newell/nixie-clock-esp32c3/clock/drivers_1.kicad_sch

## KiCad design clock/drivers_1.kicad_sch (2024-07-15)

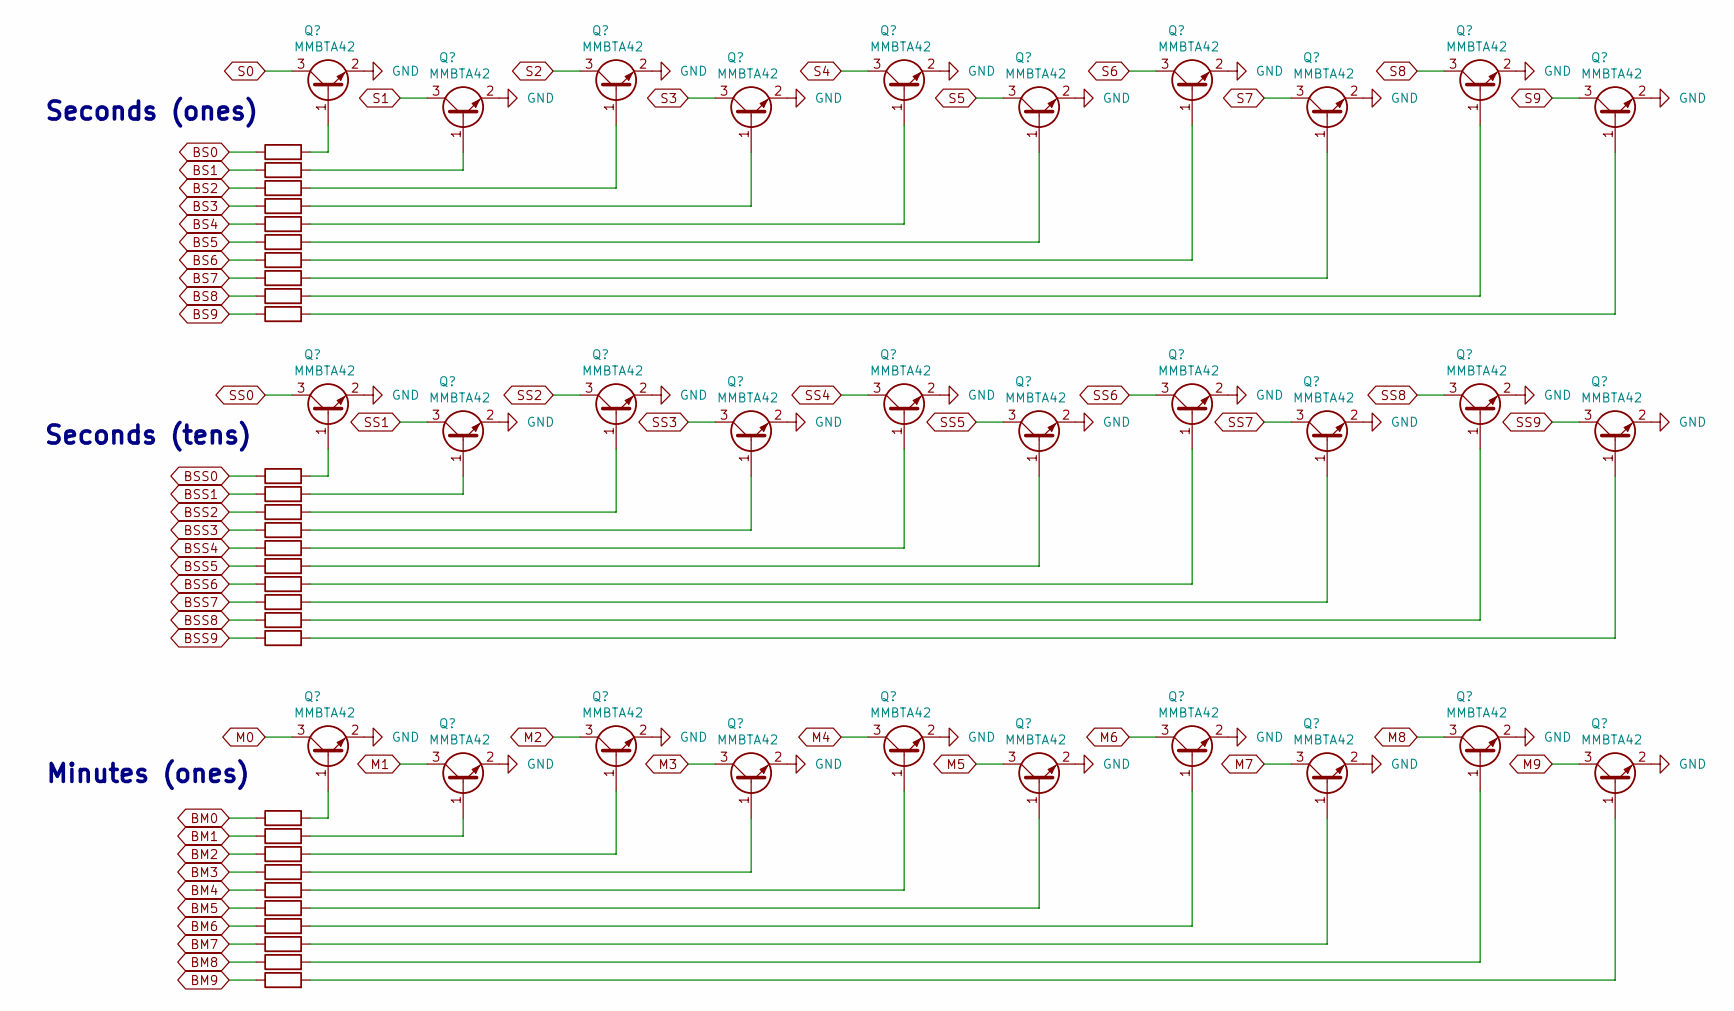
[picture p11: schematic drivers_1.kicad_sch]

Parts:
Q36, Q37, Q38, Q39, Q40, Q41, Q42, Q43, Q44, Q45, Q46, Q47, Q48, Q49, Q50, Q51, Q52, Q53, Q54, Q55, Q56, Q57, Q58, Q59, Q60, Q61, Q62, Q63, Q64, Q65: MMBTA42; SOT-23
R57, R58, R59, R60, R61, R62, R63, R64, R65, R66, R67, R68, R69, R70, R71, R72, R73, R74, R75, R76, R77, R78, R79, R80, R81, R82, R83, R84, R85, R86: 10k; R_0805_2012Metric_Pad1.20x1.40mm_HandSolder; Manufacturer_Part_Number RC0805FR-0710KL

Connections:
BM0: R77.1
BM1: R78.1
BM2: R79.1
BM3: R80.1
BM4: R81.1
BM5: R82.1
BM6: R83.1
BM7: R84.1
BM8: R85.1
BM9: R86.1
BS0: R57.1
BS1: R58.1
BS2: R59.1
BS3: R60.1
BS4: R61.1
BS5: R62.1
BS6: R63.1
BS7: R64.1
BS8: R65.1
BS9: R66.1
BSS0: R67.1
BSS1: R68.1
BSS2: R69.1
BSS3: R70.1
BSS4: R71.1
BSS5: R72.1
BSS6: R73.1
BSS7: R74.1
BSS8: R75.1
BSS9: R76.1
GND: Q36.2 (E), Q37.2 (E), Q38.2 (E), Q39.2 (E), Q40.2 (E), Q41.2 (E), Q42.2 (E), Q43.2 (E), Q44.2 (E), Q45.2 (E), Q46.2 (E), Q47.2 (E), Q48.2 (E), Q49.2 (E), Q50.2 (E), Q51.2 (E), Q52.2 (E), Q53.2 (E), Q54.2 (E), Q55.2 (E), Q56.2 (E), Q57.2 (E), Q58.2 (E), Q59.2 (E), Q60.2 (E), Q61.2 (E), Q62.2 (E), Q63.2 (E), Q64.2 (E), Q65.2 (E)
M0: Q38.3 (C)
M1: Q41.3 (C)
M2: Q44.3 (C)
M3: Q47.3 (C)
M4: Q50.3 (C)
M5: Q53.3 (C)
M6: Q56.3 (C)
M7: Q59.3 (C)
M8: Q62.3 (C)
M9: Q65.3 (C)
unnamed: Q36.1 (B), R57.2
unnamed: Q37.1 (B), R67.2
unnamed: Q38.1 (B), R77.2
unnamed: Q39.1 (B), R58.2
unnamed: Q40.1 (B), R68.2
unnamed: Q41.1 (B), R78.2
unnamed: Q42.1 (B), R59.2
unnamed: Q43.1 (B), R69.2
unnamed: Q44.1 (B), R79.2
unnamed: Q45.1 (B), R60.2
unnamed: Q46.1 (B), R70.2
unnamed: Q47.1 (B), R80.2
unnamed: Q48.1 (B), R61.2
unnamed: Q49.1 (B), R71.2
unnamed: Q50.1 (B), R81.2
unnamed: Q51.1 (B), R62.2
unnamed: Q52.1 (B), R72.2
unnamed: Q53.1 (B), R82.2
unnamed: Q54.1 (B), R63.2
unnamed: Q55.1 (B), R73.2
unnamed: Q56.1 (B), R83.2
unnamed: Q57.1 (B), R64.2
unnamed: Q58.1 (B), R74.2
unnamed: Q59.1 (B), R84.2
unnamed: Q60.1 (B), R65.2
unnamed: Q61.1 (B), R75.2
unnamed: Q62.1 (B), R85.2
unnamed: Q63.1 (B), R66.2
unnamed: Q64.1 (B), R76.2
unnamed: Q65.1 (B), R86.2
S0: Q36.3 (C)
S1: Q39.3 (C)
S2: Q42.3 (C)
S3: Q45.3 (C)
S4: Q48.3 (C)
S5: Q51.3 (C)
S6: Q54.3 (C)
S7: Q57.3 (C)
S8: Q60.3 (C)
S9: Q63.3 (C)
SS0: Q37.3 (C)
SS1: Q40.3 (C)
SS2: Q43.3 (C)
SS3: Q46.3 (C)
SS4: Q49.3 (C)
SS5: Q52.3 (C)
SS6: Q55.3 (C)
SS7: Q58.3 (C)
SS8: Q61.3 (C)
SS9: Q64.3 (C)

Notes on the sheet:
Minutes (ones)
Seconds (ones)
Seconds (tens)
