newell/nixie-clock-esp32c3/clock/drivers_2.kicad_sch

## KiCad design clock/drivers_2.kicad_sch (2024-07-15)

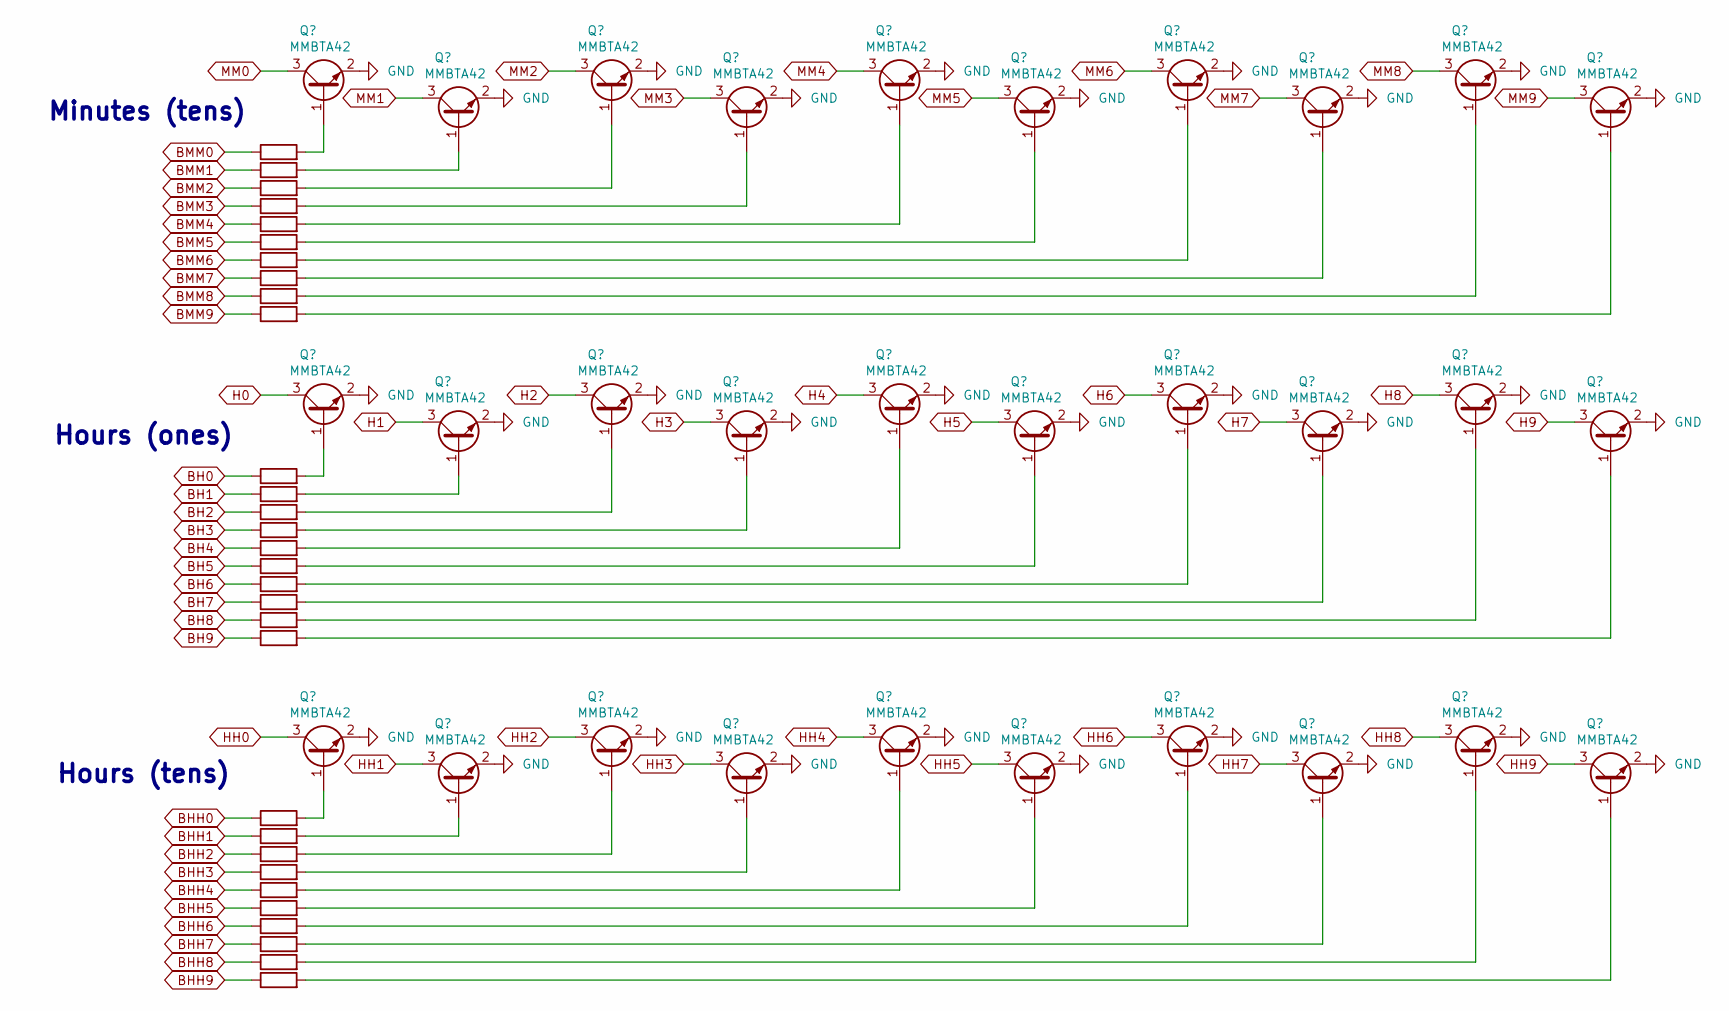
[picture p12: schematic drivers_2.kicad_sch]

Parts:
Q1, Q2, Q3, Q4, Q5, Q6, Q7, Q8, Q9, Q10, Q11, Q12, Q13, Q14, Q15, Q16, Q17, Q18, Q19, Q20, Q21, Q22, Q23, Q24, Q25, Q26, Q27, Q28, Q29, Q30: MMBTA42; SOT-23
R9, R10, R11, R12, R13, R14, R15, R16, R17, R18, R19, R20, R21, R22, R23, R24, R25, R26, R27, R28, R29, R30, R31, R32, R33, R34, R35, R36, R37, R38: 10k; R_0805_2012Metric_Pad1.20x1.40mm_HandSolder; Manufacturer_Part_Number RC0805FR-0710KL

Connections:
BH0: R19.1
BH1: R20.1
BH2: R21.1
BH3: R22.1
BH4: R23.1
BH5: R24.1
BH6: R25.1
BH7: R26.1
BH8: R27.1
BH9: R28.1
BHH0: R29.1
BHH1: R30.1
BHH2: R31.1
BHH3: R32.1
BHH4: R33.1
BHH5: R34.1
BHH6: R35.1
BHH7: R36.1
BHH8: R37.1
BHH9: R38.1
BMM0: R9.1
BMM1: R10.1
BMM2: R11.1
BMM3: R12.1
BMM4: R13.1
BMM5: R14.1
BMM6: R15.1
BMM7: R16.1
BMM8: R17.1
BMM9: R18.1
GND: Q1.2 (E), Q2.2 (E), Q3.2 (E), Q4.2 (E), Q5.2 (E), Q6.2 (E), Q7.2 (E), Q8.2 (E), Q9.2 (E), Q10.2 (E), Q11.2 (E), Q12.2 (E), Q13.2 (E), Q14.2 (E), Q15.2 (E), Q16.2 (E), Q17.2 (E), Q18.2 (E), Q19.2 (E), Q20.2 (E), Q21.2 (E), Q22.2 (E), Q23.2 (E), Q24.2 (E), Q25.2 (E), Q26.2 (E), Q27.2 (E), Q28.2 (E), Q29.2 (E), Q30.2 (E)
H0: Q2.3 (C)
H1: Q5.3 (C)
H2: Q8.3 (C)
H3: Q11.3 (C)
H4: Q14.3 (C)
H5: Q17.3 (C)
H6: Q20.3 (C)
H7: Q23.3 (C)
H8: Q26.3 (C)
H9: Q29.3 (C)
HH0: Q3.3 (C)
HH1: Q6.3 (C)
HH2: Q9.3 (C)
HH3: Q12.3 (C)
HH4: Q15.3 (C)
HH5: Q18.3 (C)
HH6: Q21.3 (C)
HH7: Q24.3 (C)
HH8: Q27.3 (C)
HH9: Q30.3 (C)
MM0: Q1.3 (C)
MM1: Q4.3 (C)
MM2: Q7.3 (C)
MM3: Q10.3 (C)
MM4: Q13.3 (C)
MM5: Q16.3 (C)
MM6: Q19.3 (C)
MM7: Q22.3 (C)
MM8: Q25.3 (C)
MM9: Q28.3 (C)
unnamed: Q1.1 (B), R9.2
unnamed: Q2.1 (B), R19.2
unnamed: Q3.1 (B), R29.2
unnamed: Q4.1 (B), R10.2
unnamed: Q5.1 (B), R20.2
unnamed: Q6.1 (B), R30.2
unnamed: Q7.1 (B), R11.2
unnamed: Q8.1 (B), R21.2
unnamed: Q9.1 (B), R31.2
unnamed: Q10.1 (B), R12.2
unnamed: Q11.1 (B), R22.2
unnamed: Q12.1 (B), R32.2
unnamed: Q13.1 (B), R13.2
unnamed: Q14.1 (B), R23.2
unnamed: Q15.1 (B), R33.2
unnamed: Q16.1 (B), R14.2
unnamed: Q17.1 (B), R24.2
unnamed: Q18.1 (B), R34.2
unnamed: Q19.1 (B), R15.2
unnamed: Q20.1 (B), R25.2
unnamed: Q21.1 (B), R35.2
unnamed: Q22.1 (B), R16.2
unnamed: Q23.1 (B), R26.2
unnamed: Q24.1 (B), R36.2
unnamed: Q25.1 (B), R17.2
unnamed: Q26.1 (B), R27.2
unnamed: Q27.1 (B), R37.2
unnamed: Q28.1 (B), R18.2
unnamed: Q29.1 (B), R28.2
unnamed: Q30.1 (B), R38.2

Notes on the sheet:
Hours (tens)
Hours (ones)
Minutes (tens)
