newell/nixie-clock-esp32c3/clock/esp32-c3.kicad_sch

## KiCad design clock/esp32-c3.kicad_sch (2024-07-15)

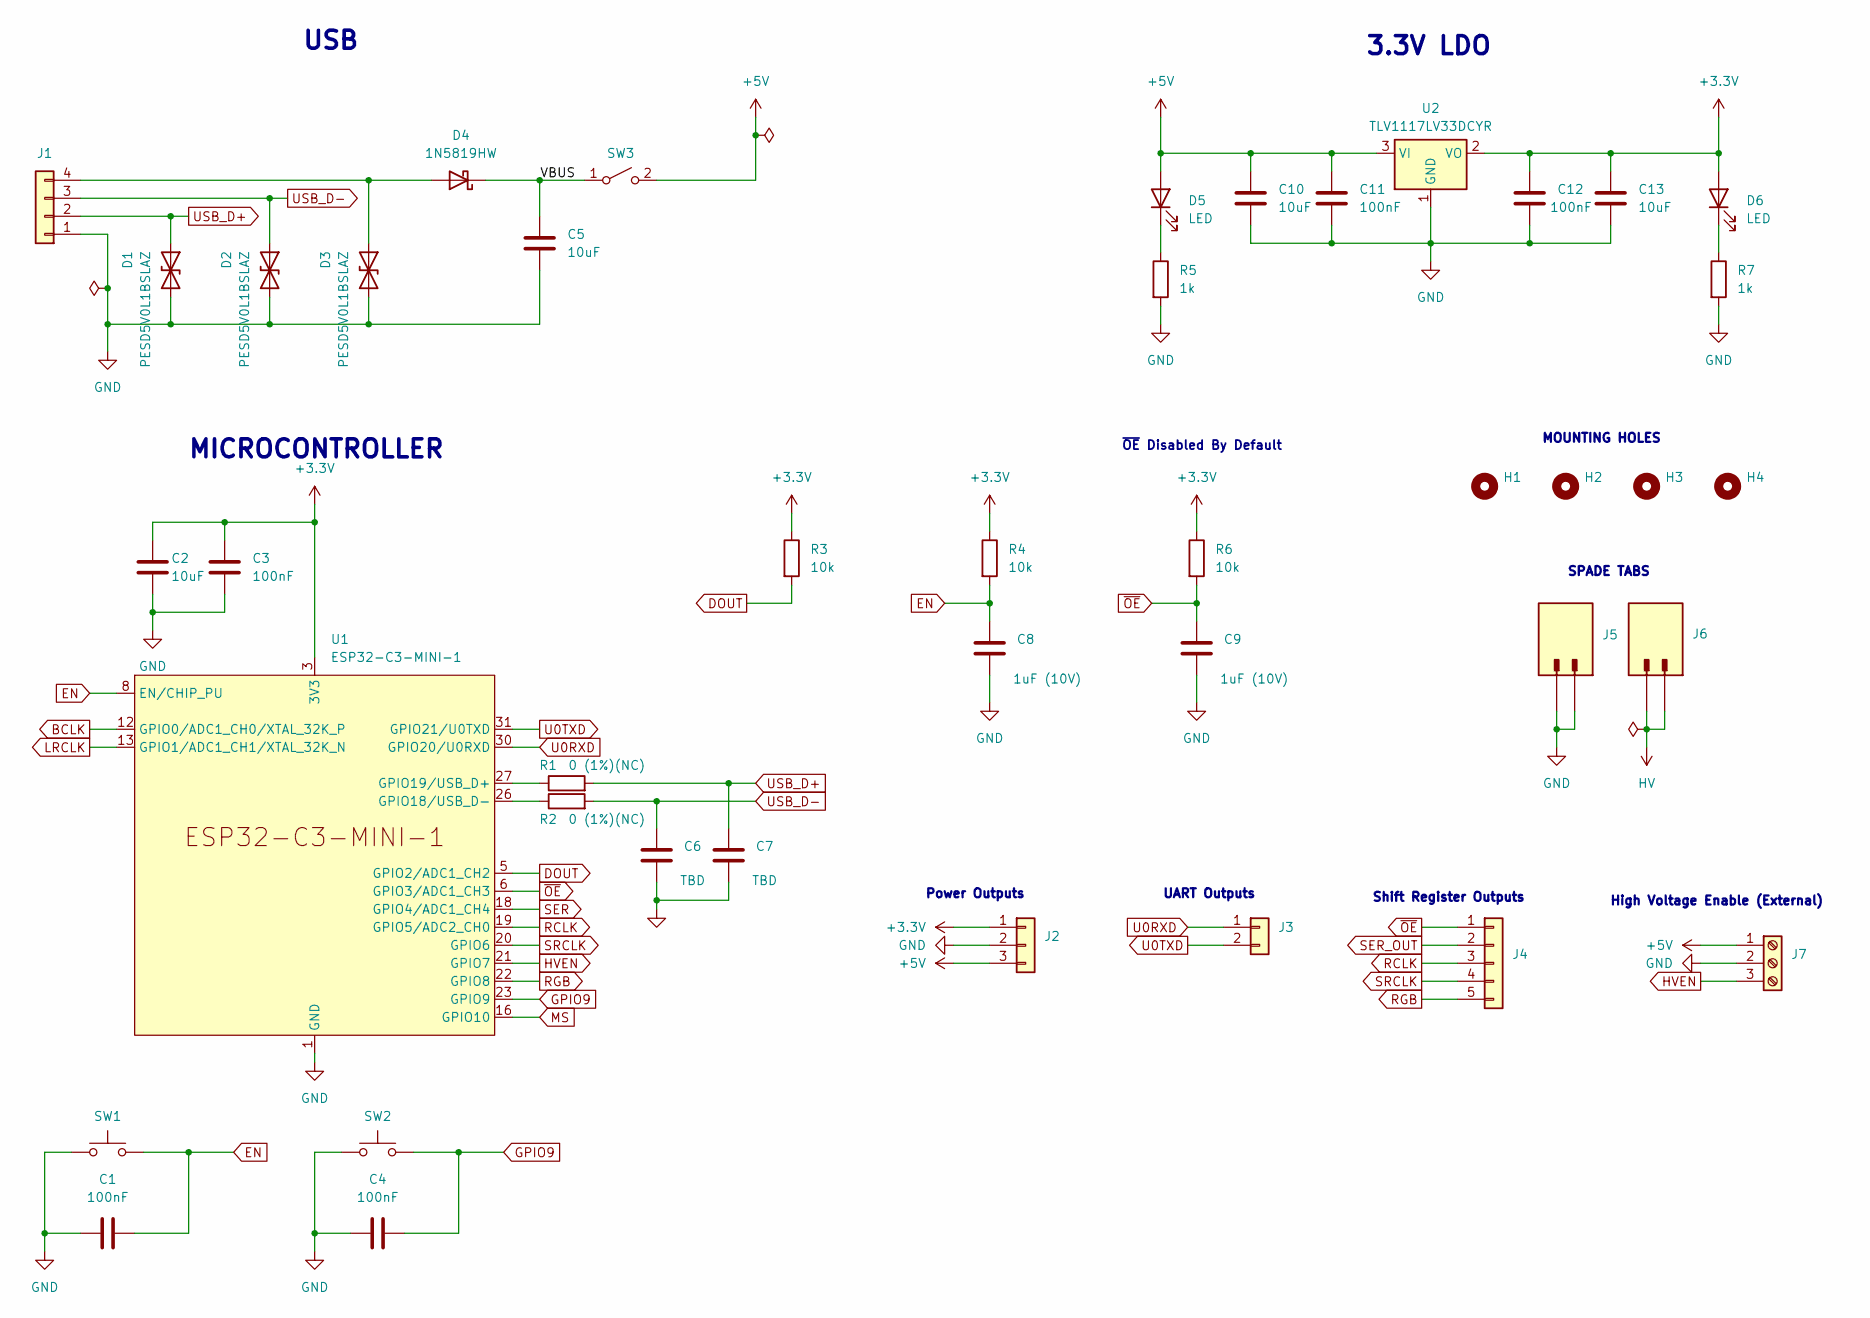
[picture p13: schematic esp32-c3.kicad_sch]

Parts:
C1, C3, C4, C11, C12: 100nF; C_0805_2012Metric_Pad1.18x1.45mm_HandSolder; Manufacturer_Part_Number CC0805JRX7R9BB104
C2, C5, C10, C13: 10uF; C_0805_2012Metric_Pad1.18x1.45mm_HandSolder; Manufacturer_Part_Number CC0805KKX5R6BB106
C6, C7: TBD; C_0805_2012Metric_Pad1.18x1.45mm_HandSolder
C8, C9: 1uF (10V); C_0805_2012Metric_Pad1.18x1.45mm_HandSolder; Manufacturer_Part_Number GRM21BR71C105KA01L
D1, D2, D3: PESD5V0L1BSLAZ; D_SOD-882; Manufacturer_Part_Number PESD5V0L1BSLAZ
D4: 1N5819HW; D_SOD-123; Manufacturer_Part_Number 1N5819HW-7-F
D5: LED; LED_0603_1608Metric_Pad1.05x0.95mm_HandSolder
D6: LED; LED_0603_1608Metric_Pad1.05x0.95mm_HandSolder; Mouser Part Number 710-150080RS75000
H1, H2, H3, H4: MountingHole; MountingHole_3.2mm_M3_ISO7380_Pad_TopBottom
J1: Conn_01x04; JST_PH_B4B-PH-K_1x04_P2.00mm_Vertical
J2: Conn_01x03; PinHeader_1x03_P2.54mm_Vertical
J3: Conn_01x02; PinHeader_1x02_P2.54mm_Vertical
J4: Conn_01x05; PinHeader_1x05_P2.54mm_Vertical
J5, J6: KEYSTONE_1287; PARTREV F
J7: Screw_Terminal_01x03; TerminalBlock_Phoenix_MKDS-1,5-3_1x03_P5.00mm_Horizontal
R1, R2: 0 (1%)(NC); R_0805_2012Metric_Pad1.20x1.40mm_HandSolder; Manufacturer_Part_Number RC0805FR-130RL
R3, R4, R6: 10k; R_0805_2012Metric_Pad1.20x1.40mm_HandSolder; Manufacturer_Part_Number RC0805FR-0710KL
R5, R7: 1k; R_0805_2012Metric_Pad1.20x1.40mm_HandSolder; Manufacturer_Part_Number RC0805FR-071KL
SW1, SW2: SW_Push; SW_Tactile_SPST_NO_Straight_CK_PTS636Sx25SMTRLFS
SW3: SW_SPST; SolderWire-0.75sqmm_1x02_P4.8mm_D1.25mm_OD2.3mm
U1: ESP32-C3-MINI-1; ESP32-C3-MINI-1_HandSoldering; Manufacturer_Part_Number ESP32-C3-MINI-1-N4
U2: TLV1117LV33DCYR; SOT-223; Manufacturer_Part_Number TLV1117LV33DCYR

Connections:
+3.3V: C2.1, C3.1, C12.1, C13.1, D6.2 (A), J2.1, R3.1, R4.1, R6.1, U1.3 (3V3), U2.2 (VO)
+5V: C10.1, C11.1, D5.2 (A), J2.3, J7.1, SW3.2 (B), U2.3 (VI)
BCLK: U1.12 (GPIO0/ADC1_CH0/XTAL_32K_P)
DOUT: R3.2, U1.5 (GPIO2/ADC1_CH2)
EN: C1.1, C8.2, R4.2, SW1.2, U1.8 (EN/CHIP_PU)
GND: C1.2, C2.2, C3.2, C4.2, C5.2, C6.1, C7.1, C8.1, C9.1, C10.2, C11.2, C12.2, C13.2, D1.2 (A2), D2.2 (A2), D3.2 (A2), J1.1, J2.2, J5.1_1, J5.1_2, J7.2, R5.2, R7.2, SW1.1, SW2.1, U1.1 (GND), U1.2 (GND), U1.11 (GND), U1.14 (GND), U1.36 (GND), U1.37 (GND), U1.38 (GND), U1.39 (GND), U1.40 (GND), U1.41 (GND), U1.42 (GND), U1.43 (GND), U1.44 (GND), U1.45 (GND), U1.46 (GND), U1.47 (GND), U1.48 (GND), U1.49 (GND), U1.50 (GND), U1.51 (GND), U1.52 (GND), U1.53 (GND), U2.1 (GND)
GPIO9: C4.1, SW2.2, U1.23 (GPIO9)
HV: J6.1_1, J6.1_2
HVEN: J7.3, U1.21 (GPIO7)
LRCLK: U1.13 (GPIO1/ADC1_CH1/XTAL_32K_N)
MS: U1.16 (GPIO10)
unnamed: D3.1 (A1), D4.2 (A), J1.4
unnamed: D5.1 (K), R5.1
unnamed: D6.1 (K), R7.1
unnamed: R1.1, U1.27 (GPIO19/USB_D+)
unnamed: R2.1, U1.26 (GPIO18/USB_D-)
RCLK: J4.3, U1.19 (GPIO5/ADC2_CH0)
RGB: J4.5, U1.22 (GPIO8)
SER: U1.18 (GPIO4/ADC1_CH4)
SER_OUT: J4.2
SRCLK: J4.4, U1.20 (GPIO6)
U0RXD: J3.1, U1.30 (GPIO20/U0RXD)
U0TXD: J3.2, U1.31 (GPIO21/U0TXD)
USB_D+: C7.2, D1.1 (A1), J1.2, R1.2
USB_D-: C6.2, D2.1 (A1), J1.3, R2.2
VBUS: C5.1, D4.1 (K), SW3.1 (A)
~OE: C9.2, J4.1, R6.2, U1.6 (GPIO3/ADC1_CH3)

Notes on the sheet:
USB
3.3V LDO
SPADE TABS
High Voltage Enable (External)
MOUNTING HOLES
Shift Register Outputs
Power Outputs
UART Outputs
MICROCONTROLLER
~{OE} Disabled By Default
