newell/nixie-clock-esp32c3/clock/nixie_tubes.kicad_sch

## KiCad design clock/nixie_tubes.kicad_sch (2024-07-15)

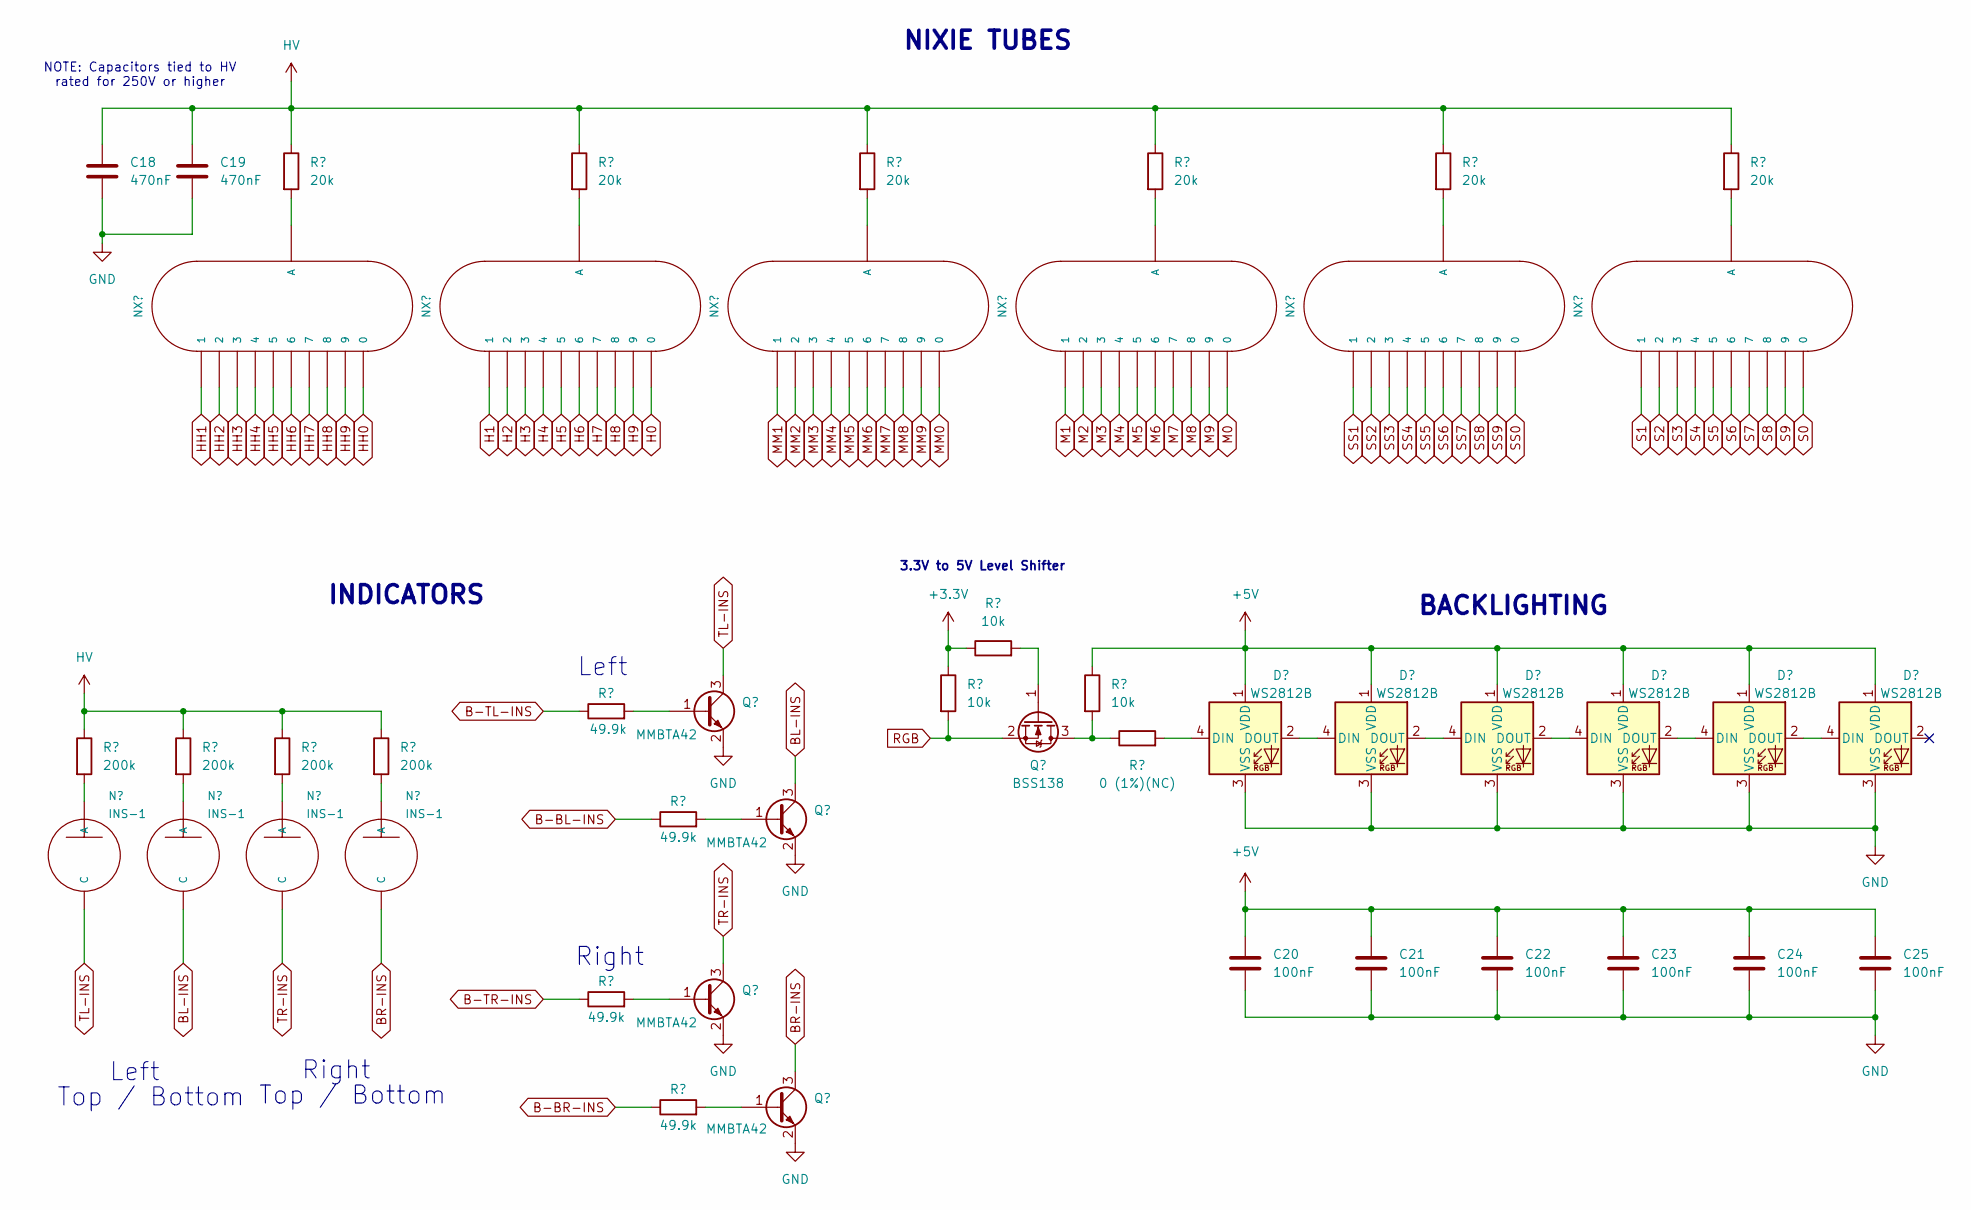
[picture p14: schematic nixie_tubes.kicad_sch]

Parts:
C18, C19: 470nF; C_1812_4532Metric_Pad1.57x3.40mm_HandSolder; Manufacturer_Part_Number CC0805JRX7R9BB104
C20, C21, C22, C23, C24, C25: 100nF; C_0805_2012Metric_Pad1.18x1.45mm_HandSolder; Manufacturer_Part_Number CC0805JRX7R9BB104
D7, D8, D9, D10, D11, D12: WS2812B; LED_WS2812B_PLCC4_5.0x5.0mm_P3.2mm
N1, N2, N3, N4: INS-1; mynixies-INS-1
NX1, NX2, NX3, NX4, NX5, NX6: IN-12A; nixies-us-IN-12-DSUB-NOHOLE
Q31, Q32, Q33, Q34: MMBTA42; SOT-23
Q35: BSS138; SOT-23; Manufacturer_Part_Number BSS138
R39, R40, R41, R43: 200k; R_0805_2012Metric_Pad1.20x1.40mm_HandSolder; Manufacturer_Part_Number RC0805FR-07200KL
R42, R44, R49, R54, R55, R56: 20k; R_0805_2012Metric_Pad1.20x1.40mm_HandSolder; Manufacturer_Part_Number RC0805JR-0720KL
R45, R46, R47, R48: 49.9k; R_0805_2012Metric_Pad1.20x1.40mm_HandSolder; Manufacturer_Part_Number RC0805FR-0749K9L
R50, R51, R52: 10k; R_0805_2012Metric_Pad1.20x1.40mm_HandSolder; Manufacturer_Part_Number RC0805FR-0710KL
R53: 0 (1%)(NC); R_0805_2012Metric_Pad1.20x1.40mm_HandSolder; Manufacturer_Part_Number RC0805FR-130RL

Connections:
+3.3V: R50.1, R51.1
+5V: C20.1, C21.1, C22.1, C23.1, C24.1, C25.1, D7.1 (VDD), D8.1 (VDD), D9.1 (VDD), D10.1 (VDD), D11.1 (VDD), D12.1 (VDD), R52.1
B-BL-INS: R47.1
B-BR-INS: R48.1
B-TL-INS: R45.1
B-TR-INS: R46.1
BL-INS: N2.P$1 (C), Q33.3 (C)
BR-INS: N4.P$1 (C), Q34.3 (C)
GND: C18.2, C19.2, C20.2, C21.2, C22.2, C23.2, C24.2, C25.2, D7.3 (VSS), D8.3 (VSS), D9.3 (VSS), D10.3 (VSS), D11.3 (VSS), D12.3 (VSS), Q31.2 (E), Q32.2 (E), Q33.2 (E), Q34.2 (E)
H0: NX2.0
H1: NX2.1
H2: NX2.2
H3: NX2.3
H4: NX2.4
H5: NX2.5
H6: NX2.6
H7: NX2.7
H8: NX2.8
H9: NX2.9
HH0: NX1.0
HH1: NX1.1
HH2: NX1.2
HH3: NX1.3
HH4: NX1.4
HH5: NX1.5
HH6: NX1.6
HH7: NX1.7
HH8: NX1.8
HH9: NX1.9
HV: C18.1, C19.1, R39.1, R40.1, R41.1, R42.1, R43.1, R44.1, R49.1, R54.1, R55.1, R56.1
M0: NX4.0
M1: NX4.1
M2: NX4.2
M3: NX4.3
M4: NX4.4
M5: NX4.5
M6: NX4.6
M7: NX4.7
M8: NX4.8
M9: NX4.9
MM0: NX3.0
MM1: NX3.1
MM2: NX3.2
MM3: NX3.3
MM4: NX3.4
MM5: NX3.5
MM6: NX3.6
MM7: NX3.7
MM8: NX3.8
MM9: NX3.9
unnamed: D7.2 (DOUT), D8.4 (DIN)
unnamed: D7.4 (DIN), R53.2
unnamed: D8.2 (DOUT), D9.4 (DIN)
unnamed: D10.2 (DOUT), D11.4 (DIN)
unnamed: D9.2 (DOUT), D10.4 (DIN)
unnamed: D11.2 (DOUT), D12.4 (DIN)
unnamed: N1.P$2 (A), R39.2
unnamed: N2.P$2 (A), R40.2
unnamed: N3.P$2 (A), R41.2
unnamed: N4.P$2 (A), R43.2
unnamed: NX1.A, R42.2
unnamed: NX2.A, R44.2
unnamed: NX3.A, R49.2
unnamed: NX4.A, R54.2
unnamed: NX5.A, R55.2
unnamed: NX6.A, R56.2
unnamed: Q31.1 (B), R45.2
unnamed: Q32.1 (B), R46.2
unnamed: Q33.1 (B), R47.2
unnamed: Q34.1 (B), R48.2
unnamed: Q35.1 (G), R51.2
unnamed: Q35.3 (D), R52.2, R53.1
RGB: Q35.2 (S), R50.2
S0: NX6.0
S1: NX6.1
S2: NX6.2
S3: NX6.3
S4: NX6.4
S5: NX6.5
S6: NX6.6
S7: NX6.7
S8: NX6.8
S9: NX6.9
SS0: NX5.0
SS1: NX5.1
SS2: NX5.2
SS3: NX5.3
SS4: NX5.4
SS5: NX5.5
SS6: NX5.6
SS7: NX5.7
SS8: NX5.8
SS9: NX5.9
TL-INS: N1.P$1 (C), Q31.3 (C)
TR-INS: N3.P$1 (C), Q32.3 (C)

Notes on the sheet:
3.3V to 5V Level Shifter
Right
BACKLIGHTING
Left
NOTE: Capacitors tied to HV rated for 250V or higher
Top / Bottom
INDICATORS
NIXIE TUBES
