newell/nixie-clock-esp32c3/clock/power.kicad_sch

## KiCad design clock/power.kicad_sch (2024-07-15)

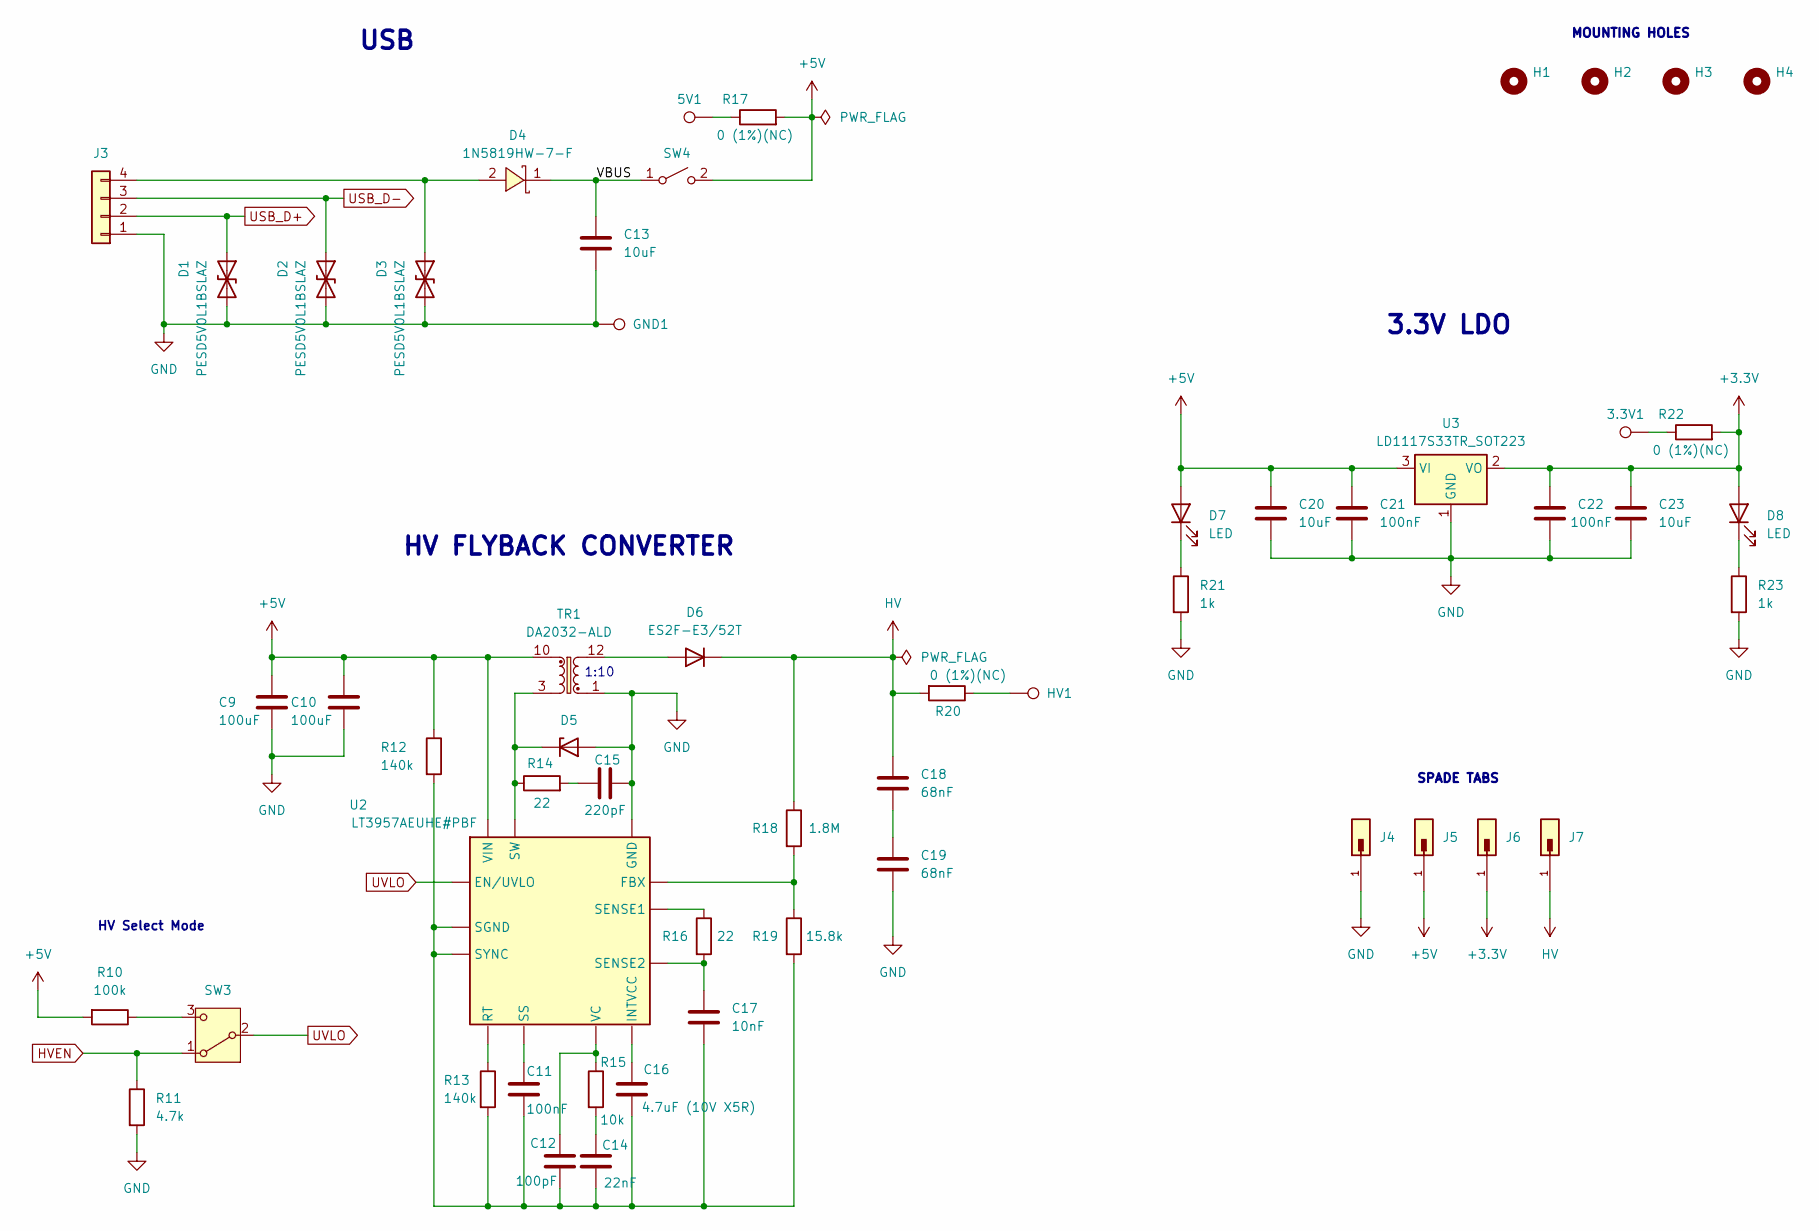
[picture p15: schematic power.kicad_sch]

Parts:
3.3V1, 5V1: TestPoint; TestPoint_Pad_D1.0mm
C9, C10: 100uF; GRM31x
C11, C21, C22: 100nF; C_0805_2012Metric_Pad1.18x1.45mm_HandSolder
C12: 100pF; C_0805_2012Metric_Pad1.18x1.45mm_HandSolder
C13, C20, C23: 10uF; C_0805_2012Metric_Pad1.18x1.45mm_HandSolder
C14: 22nF; C_0805_2012Metric_Pad1.18x1.45mm_HandSolder
C15: 220pF; C_0805_2012Metric_Pad1.18x1.45mm_HandSolder
C16: 4.7uF (10V X5R); C_0805_2012Metric_Pad1.18x1.45mm_HandSolder
C17: 10nF; C_0805_2012Metric_Pad1.18x1.45mm_HandSolder
C18, C19: 68nF; GRM43x; Mouser Part Number 81-GRM43QR72J683KW01
D1, D2, D3: PESD5V0L1BSLAZ; D_SOD-882
D4: 1N5819HW-7-F; D_SOD-123F; LCSC Part C82544
D5: MMSZ5258B; D_SOD-123F
D6: ES2F-E3/52T; D_SMB_Handsoldering
D7: LED; LED_0603_1608Metric_Pad1.05x0.95mm_HandSolder
D8: LED; LED_0603_1608Metric_Pad1.05x0.95mm_HandSolder; Mouser Part Number 710-150080RS75000
GND1: TestPoint; TestPoint_Pad_D1.0mm
H1, H2, H3, H4: MountingHole; MountingHole_3.2mm_M3_ISO7380_Pad_TopBottom
HV1: TestPoint; TestPoint_Pad_D1.0mm
J3: Conn_01x04; JST_PH_B4B-PH-K_1x04_P2.00mm_Vertical
J4, J5, J6, J7: KEYSTONE_spade_tab; PARTREV D
R10: 100k; R_0805_2012Metric_Pad1.20x1.40mm_HandSolder
R11: 4.7k; R_0805_2012Metric_Pad1.20x1.40mm_HandSolder
R12, R13: 140k; R_0805_2012Metric_Pad1.20x1.40mm_HandSolder
R14, R16: 22; R_0805_2012Metric_Pad1.20x1.40mm_HandSolder
R15: 10k; R_0805_2012Metric_Pad1.20x1.40mm_HandSolder
R17, R20, R22: 0 (1%)(NC); R_0805_2012Metric_Pad1.20x1.40mm_HandSolder
R18: 1.8M; RESC3116X65N; Mouser Part Number 603-RC1206FR-071M8L
R19: 15.8k; R_0805_2012Metric_Pad1.20x1.40mm_HandSolder
R21, R23: 1k; R_0805_2012Metric_Pad1.20x1.40mm_HandSolder
SW3: SW_SPDT; SW_SPDT_PCM12
SW4: SW_SPST; SolderWire-0.75sqmm_1x02_P4.8mm_D1.25mm_OD2.3mm
TR1: DA2032-ALD; SOP250P2197X889-12N
U2: LT3957AEUHE#PBF; LT3958EUHETRPBF; Manufacturer_Part_Number LT3957AEUHE#PBF
U3: LD1117S33TR_SOT223; TO-220-3_Vertical

Connections:
+3.3V: C22.1, C23.1, D8.2 (A), J6.1, R22.2, U3.2 (VO)
+5V: C9.1, C10.1, C20.1, C21.1, D7.2 (A), J5.1, R10.2, R12.1, R17.2, SW4.2 (B), TR1.7, TR1.8, TR1.9, TR1.10, U2.27 (VIN), U3.3 (VI)
GND: C9.2, C10.2, C13.2, C15.2, C19.2, C20.2, C21.2, C22.2, C23.2, D1.2 (A2), D2.2 (A2), D3.2 (A2), D5.2 (A), GND1.1, J3.1, J4.1, R11.2, R21.2, R23.2, TR1.1, U2.12 (GND), U2.13 (GND), U2.14 (GND), U2.15 (GND), U2.16 (GND), U2.17 (GND), U3.1 (GND)
HV: C18.1, D6.1 (K), J7.1, R18.1, R20.2
HVEN: R11.1, SW3.1 (A)
unnamed: 3.3V1.1, R22.1
unnamed: 5V1.1, R17.1
unnamed: C11.1, U2.32 (SS)
unnamed: C11.2, C12.2, C14.2, C16.2, C17.2, R12.2, R13.2, R19.2, U2.4 (SGND), U2.23 (SGND), U2.24 (SGND), U2.34 (SYNC), U2.37 (SGND)
unnamed: C12.1, R15.1, U2.30 (VC)
unnamed: C14.1, R15.2
unnamed: C15.1, R14.2
unnamed: C16.1, U2.28 (INTVCC)
unnamed: C17.1, R16.2, U2.3 (SENSE2)
unnamed: C18.2, C19.1
unnamed: D3.1 (A1), D4.2 (A), J3.4
unnamed: D5.1 (K), R14.1, TR1.3, TR1.4, TR1.5, TR1.6, U2.8 (SW), U2.9 (SW), U2.20 (SW), U2.21 (SW), U2.38 (SW)
unnamed: D6.2 (A), TR1.12
unnamed: D7.1 (K), R21.1
unnamed: D8.1 (K), R23.1
unnamed: HV1.1, R20.1
unnamed: R10.1, SW3.3 (C)
unnamed: R13.1, U2.33 (RT)
unnamed: R16.1, U2.6 (SENSE1)
unnamed: R18.2, R19.1, U2.31 (FBX)
unnamed: U2.1 (NC), U2.2 (NC), U2.10 (NC), U2.35 (NC), U2.36 (NC)
USB_D+: D1.1 (A1), J3.2
USB_D-: D2.1 (A1), J3.3
UVLO: SW3.2 (B), U2.25 (EN/UVLO)
VBUS: C13.1, D4.1 (K), SW4.1 (A)

Notes on the sheet:
MOUNTING HOLES
3.3V LDO
1:10
HV Select Mode
USB
SPADE TABS
HV FLYBACK CONVERTER
