newell/nixie-clock-esp32c3/clock/shift_registers.kicad_sch

## KiCad design clock/shift_registers.kicad_sch (2024-07-15)

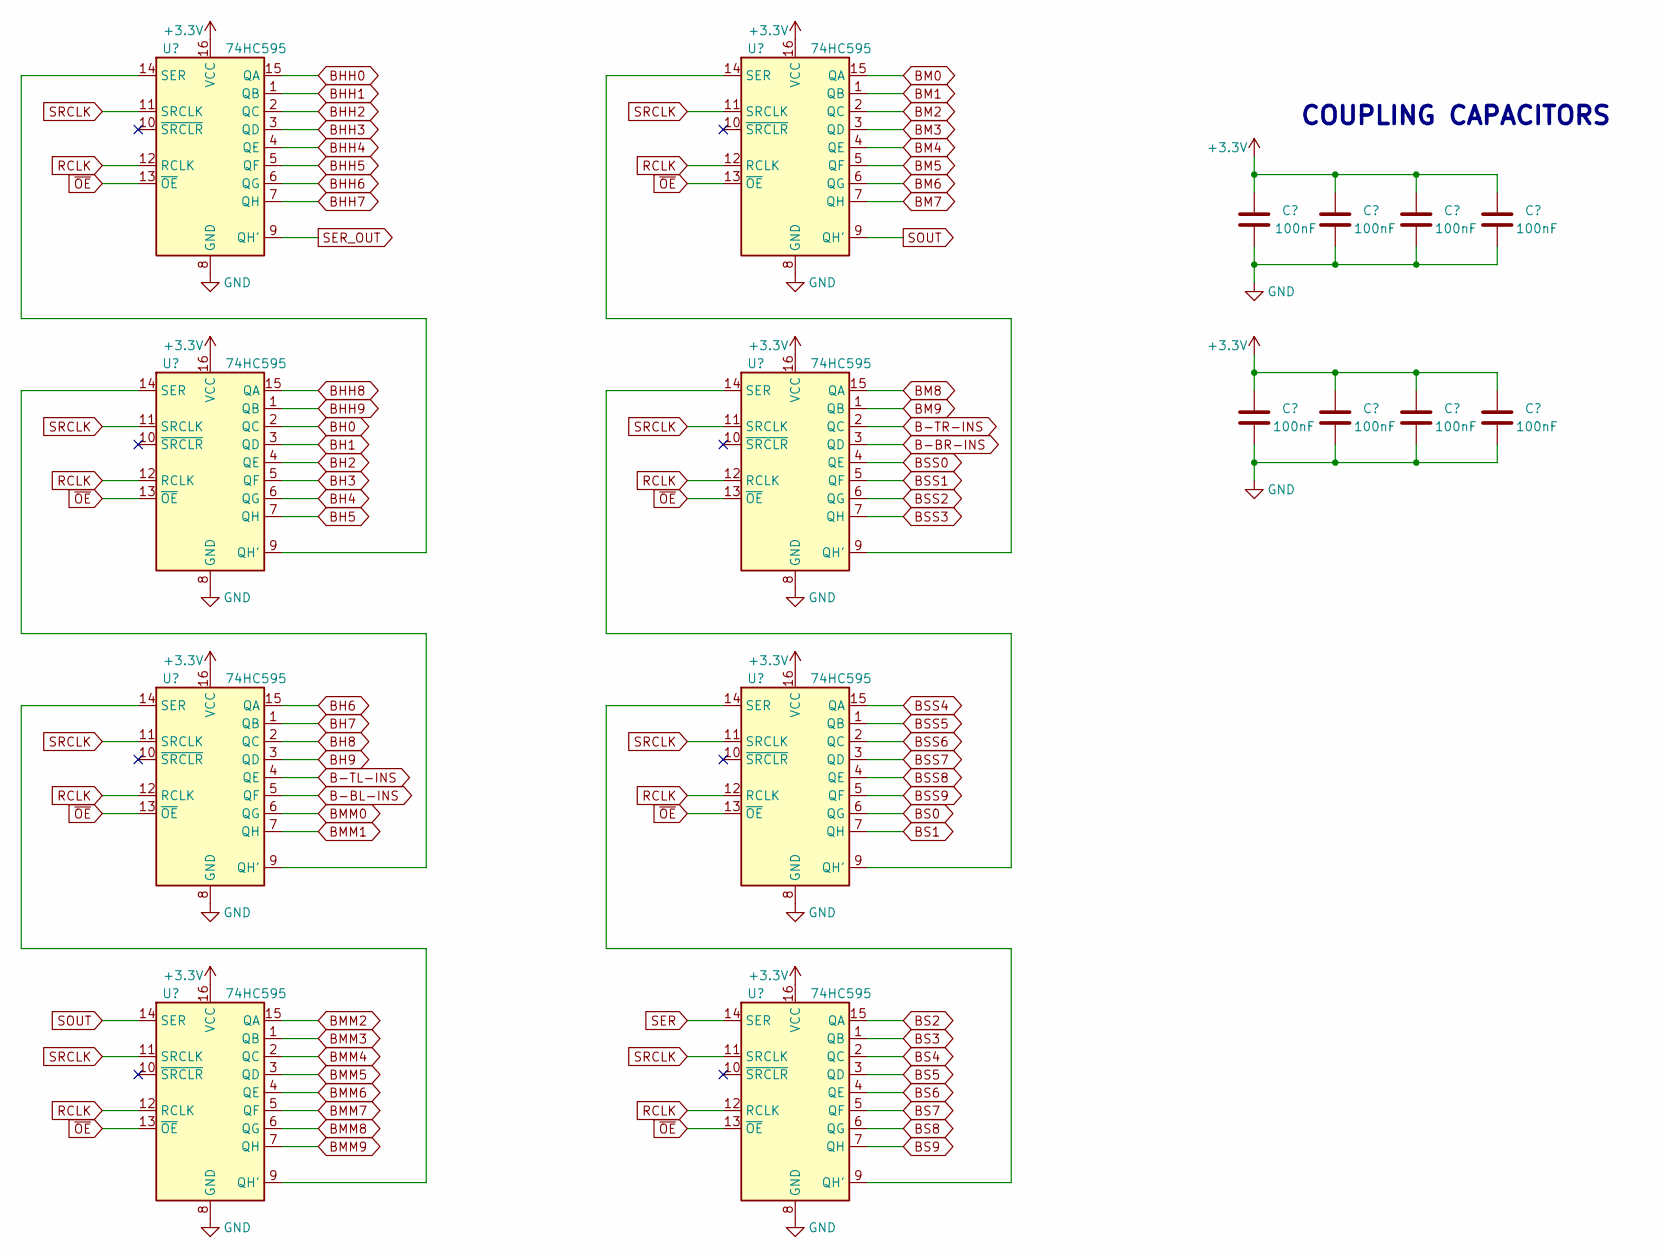
[picture p16: schematic shift_registers.kicad_sch]

Parts:
C26, C27, C28, C29, C30, C31, C32, C33: 100nF; C_0805_2012Metric_Pad1.18x1.45mm_HandSolder; Manufacturer_Part_Number CC0805JRX7R9BB104
U4, U5, U6, U7, U8, U9, U10, U11: 74HC595; SOIC-16_3.9x9.9mm_P1.27mm

Connections:
+3.3V: C26.1, C27.1, C28.1, C29.1, C30.1, C31.1, C32.1, C33.1, U4.16 (VCC), U5.16 (VCC), U6.16 (VCC), U7.16 (VCC), U8.16 (VCC), U9.16 (VCC), U10.16 (VCC), U11.16 (VCC)
B-BL-INS: U6.5 (QF)
B-BR-INS: U9.3 (QD)
B-TL-INS: U6.4 (QE)
B-TR-INS: U9.2 (QC)
BH0: U5.2 (QC)
BH1: U5.3 (QD)
BH2: U5.4 (QE)
BH3: U5.5 (QF)
BH4: U5.6 (QG)
BH5: U5.7 (QH)
BH6: U6.15 (QA)
BH7: U6.1 (QB)
BH8: U6.2 (QC)
BH9: U6.3 (QD)
BHH0: U4.15 (QA)
BHH1: U4.1 (QB)
BHH2: U4.2 (QC)
BHH3: U4.3 (QD)
BHH4: U4.4 (QE)
BHH5: U4.5 (QF)
BHH6: U4.6 (QG)
BHH7: U4.7 (QH)
BHH8: U5.15 (QA)
BHH9: U5.1 (QB)
BM0: U8.15 (QA)
BM1: U8.1 (QB)
BM2: U8.2 (QC)
BM3: U8.3 (QD)
BM4: U8.4 (QE)
BM5: U8.5 (QF)
BM6: U8.6 (QG)
BM7: U8.7 (QH)
BM8: U9.15 (QA)
BM9: U9.1 (QB)
BMM0: U6.6 (QG)
BMM1: U6.7 (QH)
BMM2: U7.15 (QA)
BMM3: U7.1 (QB)
BMM4: U7.2 (QC)
BMM5: U7.3 (QD)
BMM6: U7.4 (QE)
BMM7: U7.5 (QF)
BMM8: U7.6 (QG)
BMM9: U7.7 (QH)
BS0: U10.6 (QG)
BS1: U10.7 (QH)
BS2: U11.15 (QA)
BS3: U11.1 (QB)
BS4: U11.2 (QC)
BS5: U11.3 (QD)
BS6: U11.4 (QE)
BS7: U11.5 (QF)
BS8: U11.6 (QG)
BS9: U11.7 (QH)
BSS0: U9.4 (QE)
BSS1: U9.5 (QF)
BSS2: U9.6 (QG)
BSS3: U9.7 (QH)
BSS4: U10.15 (QA)
BSS5: U10.1 (QB)
BSS6: U10.2 (QC)
BSS7: U10.3 (QD)
BSS8: U10.4 (QE)
BSS9: U10.5 (QF)
GND: C26.2, C27.2, C28.2, C29.2, C30.2, C31.2, C32.2, C33.2, U4.8 (GND), U5.8 (GND), U6.8 (GND), U7.8 (GND), U8.8 (GND), U9.8 (GND), U10.8 (GND), U11.8 (GND)
unnamed: U4.14 (SER), U5.9 (QH')
unnamed: U5.14 (SER), U6.9 (QH')
unnamed: U6.14 (SER), U7.9 (QH')
unnamed: U8.14 (SER), U9.9 (QH')
unnamed: U9.14 (SER), U10.9 (QH')
unnamed: U10.14 (SER), U11.9 (QH')
RCLK: U4.12 (RCLK), U5.12 (RCLK), U6.12 (RCLK), U7.12 (RCLK), U8.12 (RCLK), U9.12 (RCLK), U10.12 (RCLK), U11.12 (RCLK)
SER: U11.14 (SER)
SER_OUT: U4.9 (QH')
SOUT: U7.14 (SER), U8.9 (QH')
SRCLK: U4.11 (SRCLK), U5.11 (SRCLK), U6.11 (SRCLK), U7.11 (SRCLK), U8.11 (SRCLK), U9.11 (SRCLK), U10.11 (SRCLK), U11.11 (SRCLK)
~OE: U4.13 (~OE), U5.13 (~OE), U6.13 (~OE), U7.13 (~OE), U8.13 (~OE), U9.13 (~OE), U10.13 (~OE), U11.13 (~OE)

Notes on the sheet:
COUPLING CAPACITORS
