newell/nixie-clock-esp32c3/clock/sound_motion.kicad_sch

## KiCad design clock/sound_motion.kicad_sch (2024-07-15)

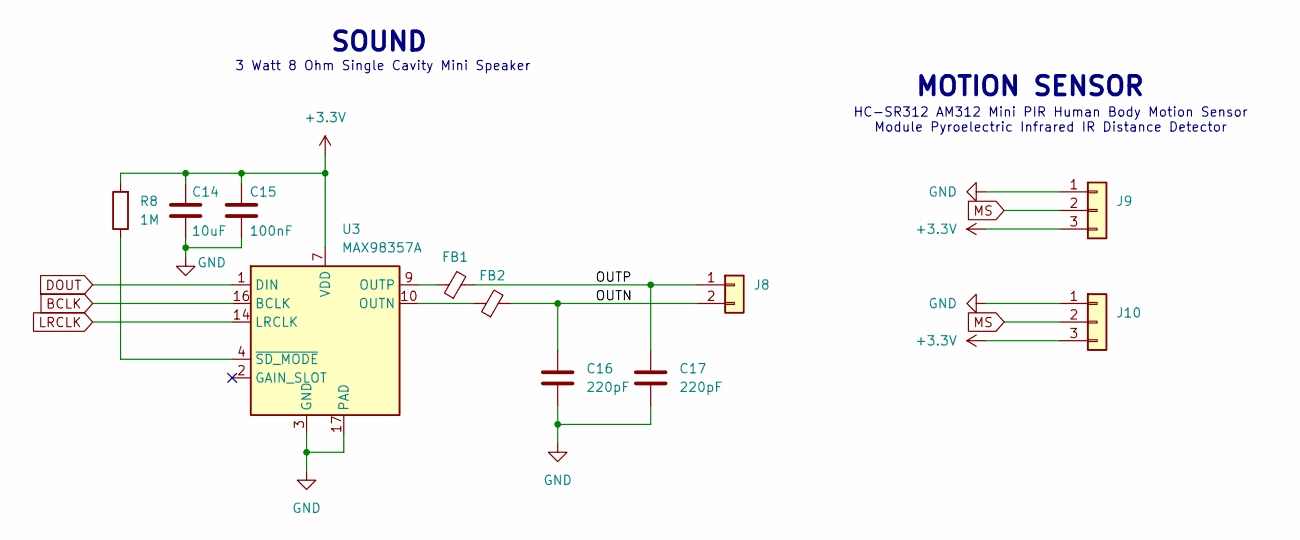
[picture p17: schematic sound_motion.kicad_sch]

Parts:
C14: 10uF; C_0805_2012Metric_Pad1.18x1.45mm_HandSolder; Manufacturer_Part_Number CC0805KKX5R6BB106
C15: 100nF; C_0805_2012Metric_Pad1.18x1.45mm_HandSolder; Manufacturer_Part_Number CC0805JRX7R9BB104
C16, C17: 220pF; C_0805_2012Metric_Pad1.18x1.45mm_HandSolder; Manufacturer_Part_Number CC0805JRNPO9BN221
FB1, FB2: FerriteBead_Small; R_0805_2012Metric_Pad1.20x1.40mm_HandSolder
J8: Conn_01x02; PinHeader_1x02_P2.54mm_Vertical
J9, J10: Conn_01x03; PinHeader_1x03_P2.54mm_Vertical
R8: 1M; R_0805_2012Metric_Pad1.20x1.40mm_HandSolder; Manufacturer_Part_Number RC0805FR-071ML
U3: MAX98357A; TQFN-16-1EP_3x3mm_P0.5mm_EP1.23x1.23mm

Connections:
+3.3V: C14.1, C15.1, J9.3, J10.3, R8.2, U3.7 (VDD), U3.8 (VDD)
BCLK: U3.16 (BCLK)
DOUT: U3.1 (DIN)
GND: C14.2, C15.2, C16.2, C17.2, J9.1, J10.1, U3.3 (GND), U3.11 (GND), U3.15 (GND), U3.17 (PAD)
LRCLK: U3.14 (LRCLK)
MS: J9.2, J10.2
unnamed: FB1.1, U3.9 (OUTP)
unnamed: FB2.1, U3.10 (OUTN)
unnamed: R8.1, U3.4 (~SD_MODE)
OUTN: C16.1, FB2.2, J8.2
OUTP: C17.1, FB1.2, J8.1

Notes on the sheet:
3 Watt 8 Ohm Single Cavity Mini Speaker
MOTION SENSOR
HC-SR312 AM312 Mini PIR Human Body Motion Sensor Module Pyroelectric Infrared IR Distance Detector
SOUND
