newell/nixie-clock-esp32c3/main/clock.h

#ifndef CLOCK_H
#define CLOCK_H

#include "freertos/FreeRTOS.h"

#define OE_PIN \
    GPIO_NUM_3  // Output Enable pin connected to the shift register (~OE)
#define DATA_PIN GPIO_NUM_4  // Data pin connected to the shift register (SER)
#define LATCH_PIN \
    GPIO_NUM_5  // Latch pin connected to the shift register (RCLK)
#define CLOCK_PIN \
    GPIO_NUM_6  // Clock pin connected to the shift register (SRCLK)
#define GPIO_OUTPUT_PIN_SEL                                        \
    ((1ULL << OE_PIN) | (1ULL << DATA_PIN) | (1ULL << LATCH_PIN) | \
     (1ULL << CLOCK_PIN))

// void slot_machine_effect(void);
void clock_init(void);
void clock_set_ram_format(int fmt);
// void clock_send_slot_machine(void);
void clock_send_slot_machine_with_leds(void);

#endif /* CLOCK_H */

// #ifndef CLOCK_H
// #define CLOCK_H

// #include "freertos/FreeRTOS.h"
// #include "freertos/semphr.h"

// #define OE_PIN      GPIO_NUM_3  // Output Enable pin connected to the shift
// register (~OE) #define DATA_PIN    GPIO_NUM_4  // Data pin connected to the
// shift register (SER) #define LATCH_PIN   GPIO_NUM_5  // Latch pin connected
// to the shift register (RCLK) #define CLOCK_PIN   GPIO_NUM_6  // Clock pin
// connected to the shift register (SRCLK) #define GPIO_OUTPUT_PIN_SEL
// ((1ULL<<OE_PIN) | (1ULL<<DATA_PIN) | (1ULL<<LATCH_PIN) | (1ULL<<CLOCK_PIN))

// extern SemaphoreHandle_t xMutex;

// void slot_machine_effect(void);
// void clock_init(void);

// #endif /* CLOCK_H */
