newell/nixie-clock-esp32c3/main/wifi_prov.h

#ifndef WIFI_PROV_H
#define WIFI_PROV_H

#define ESP_MAXIMUM_RETRY CONFIG_ESP_MAXIMUM_RETRY

#if CONFIG_ESP_WPA3_SAE_PWE_HUNT_AND_PECK
#define ESP_WIFI_SAE_MODE WPA3_SAE_PWE_HUNT_AND_PECK
#define H2E_IDENTIFIER ""
#elif CONFIG_ESP_WPA3_SAE_PWE_HASH_TO_ELEMENT
#define ESP_WIFI_SAE_MODE WPA3_SAE_PWE_HASH_TO_ELEMENT
#define H2E_IDENTIFIER CONFIG_ESP_WIFI_PW_ID
#elif CONFIG_ESP_WPA3_SAE_PWE_BOTH
#define ESP_WIFI_SAE_MODE WPA3_SAE_PWE_BOTH
#define H2E_IDENTIFIER CONFIG_ESP_WIFI_PW_ID
#endif
#if CONFIG_ESP_WIFI_AUTH_OPEN
#define ESP_WIFI_SCAN_AUTH_MODE_THRESHOLD WIFI_AUTH_OPEN
#elif CONFIG_ESP_WIFI_AUTH_WEP
#define ESP_WIFI_SCAN_AUTH_MODE_THRESHOLD WIFI_AUTH_WEP
#elif CONFIG_ESP_WIFI_AUTH_WPA_PSK
#define ESP_WIFI_SCAN_AUTH_MODE_THRESHOLD WIFI_AUTH_WPA_PSK
#elif CONFIG_ESP_WIFI_AUTH_WPA2_PSK
#define ESP_WIFI_SCAN_AUTH_MODE_THRESHOLD WIFI_AUTH_WPA2_PSK
#elif CONFIG_ESP_WIFI_AUTH_WPA_WPA2_PSK
#define ESP_WIFI_SCAN_AUTH_MODE_THRESHOLD WIFI_AUTH_WPA_WPA2_PSK
#elif CONFIG_ESP_WIFI_AUTH_WPA3_PSK
#define ESP_WIFI_SCAN_AUTH_MODE_THRESHOLD WIFI_AUTH_WPA3_PSK
#elif CONFIG_ESP_WIFI_AUTH_WPA2_WPA3_PSK
#define ESP_WIFI_SCAN_AUTH_MODE_THRESHOLD WIFI_AUTH_WPA2_WPA3_PSK
#elif CONFIG_ESP_WIFI_AUTH_WAPI_PSK
#define ESP_WIFI_SCAN_AUTH_MODE_THRESHOLD WIFI_AUTH_WAPI_PSK
#endif

/* The event group allows multiple bits for each event, but we only care about
 * two events:
 * - we are connected to the AP with an IP
 * - we failed to connect after the maximum amount of retries */
#define WIFI_CONNECTED_BIT BIT0
#define WIFI_FAIL_BIT BIT1

#define PROV_SEC2_USERNAME "wifiprov"
#define PROV_SEC2_PWD "abcd1234"

void wifi_prov_init(void);

#endif /* WIFI_PROV_H */
